mason334/J20-fighter-jet-FPV-simflight-cockpit/3d模型 2024_4_19/座舱3d模型/main screen left side panel.png

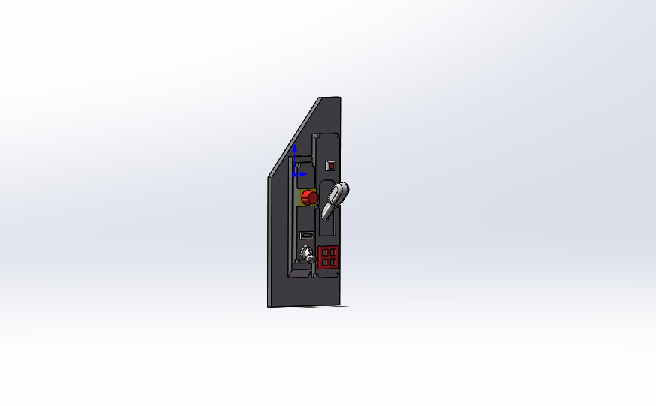
3d模型 2024_4_19/座舱3d模型/main screen left side panel.png
