mason334/J20-fighter-jet-FPV-simflight-cockpit/3d模型 2024_4_19/座舱3d模型/舱盖 适配 含进气道 座舱.png

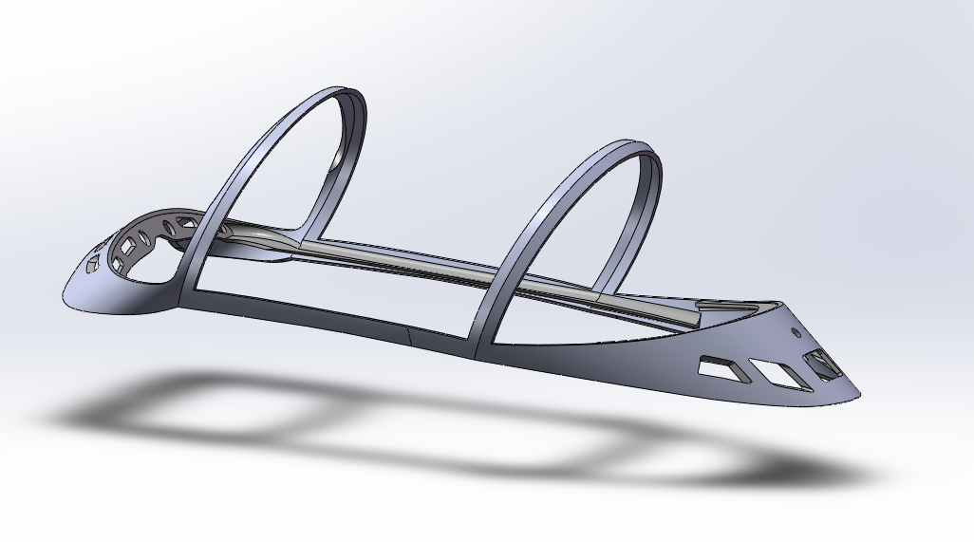
3d模型 2024_4_19/座舱3d模型/舱盖 适配 含进气道 座舱.png
