mason334/J20-fighter-jet-FPV-simflight-cockpit/3d模型 2024_4_19/座舱3d模型/装饰hud 适配 spi tft版座舱.png

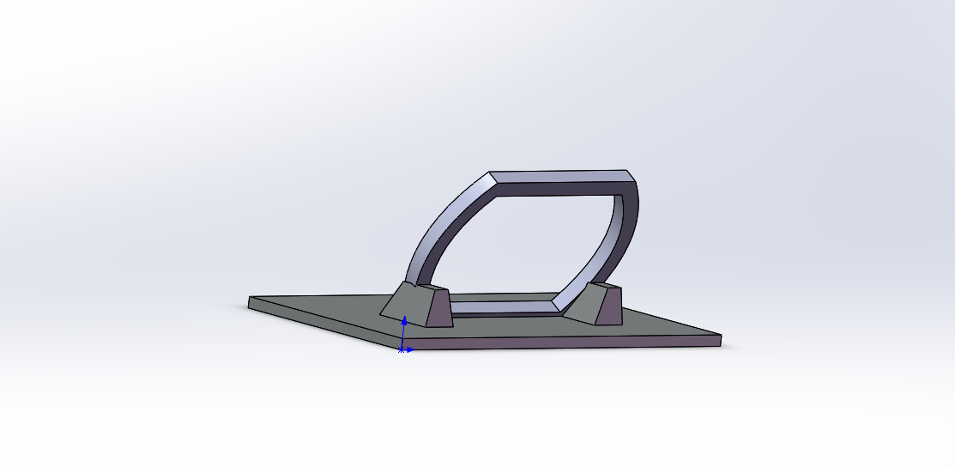
3d模型 2024_4_19/座舱3d模型/装饰hud 适配 spi tft版座舱.png
