mason334/J20-fighter-jet-FPV-simflight-cockpit/3d模型 2024_4_19/新小胖3d配件/right_airfol.png

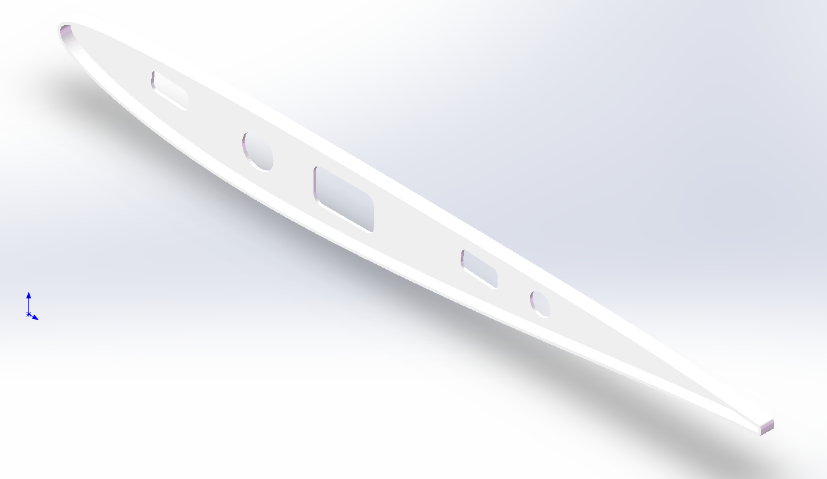
3d模型 2024_4_19/新小胖3d配件/right_airfol.png
