mason334/J20-fighter-jet-FPV-simflight-cockpit/3d模型 2024_4_19/座舱3d模型/光学hud 适配 lilygo amoled版 座舱.STEP

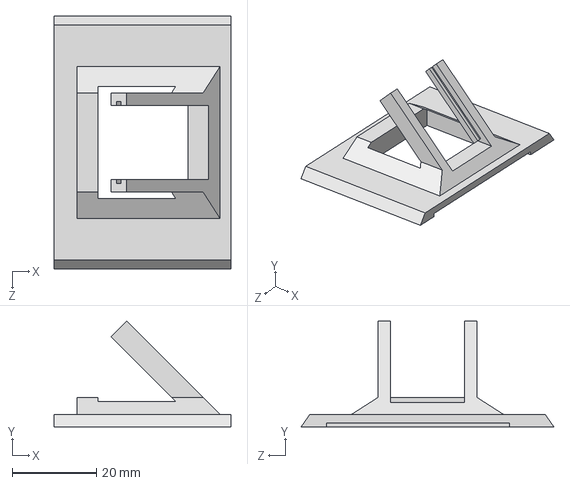
[picture p40: CAD file, 2024-04-19]
3d模型 2024_4_19/座舱3d模型/光学hud 适配 lilygo amoled版 座舱.STEP
41.9 x 25.1 x 60.0 mm
