mason334/J20-fighter-jet-FPV-simflight-cockpit/3d模型 2024_4_19/新小胖3d配件/9g servo adapter.STEP

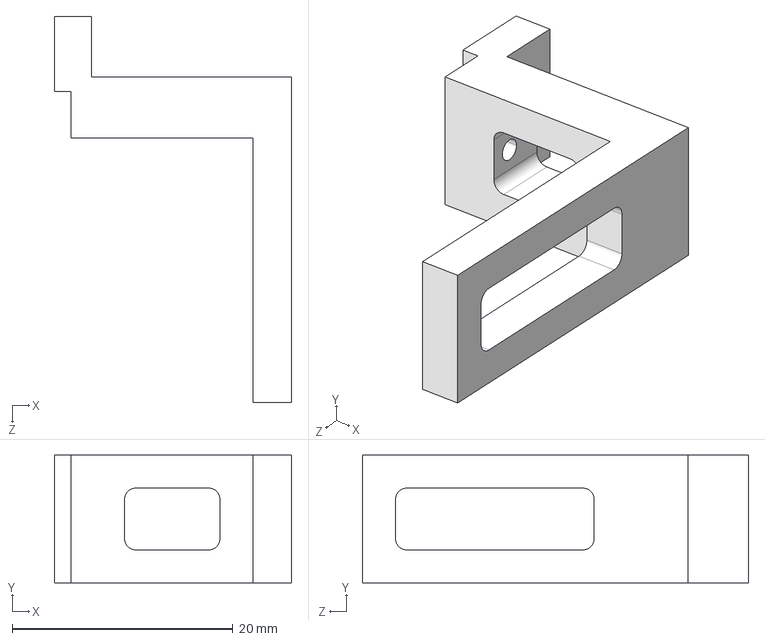
[picture p41: CAD file, 2024-04-19]
3d模型 2024_4_19/新小胖3d配件/9g servo adapter.STEP
21.5 x 11.6 x 35.0 mm
