mason334/J20-fighter-jet-FPV-simflight-cockpit/J20座舱3D模型 适配新小胖 2025-4/新小胖 j20座舱 3D模型 2025-4/舱盖.STEP

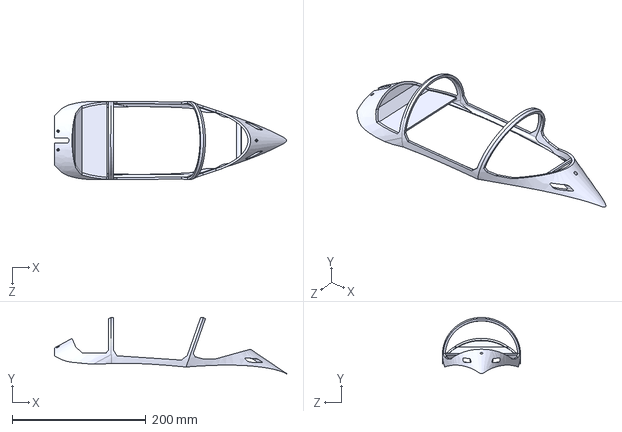
[picture p42: CAD file, 2025-04-10]
J20座舱3D模型 适配新小胖 2025-4/新小胖 j20座舱 3D模型 2025-4/舱盖.STEP
347.2 x 83.8 x 116.9 mm
