mason334/J20-fighter-jet-FPV-simflight-cockpit/3d模型 2024_4_19/座舱3d模型/left side control panel.STEP

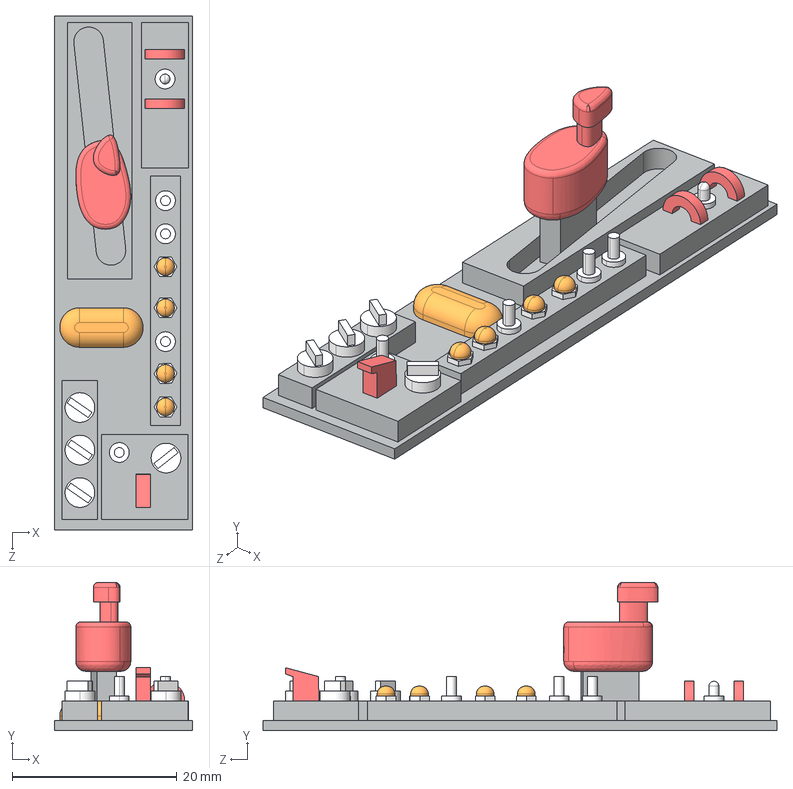
[picture p43: CAD file, 2024-04-19]
3d模型 2024_4_19/座舱3d模型/left side control panel.STEP
16.8 x 18.0 x 62.4 mm
