mason334/J20-fighter-jet-FPV-simflight-cockpit/3d模型 2024_4_19/新小胖3d配件/Motor_mount.STL

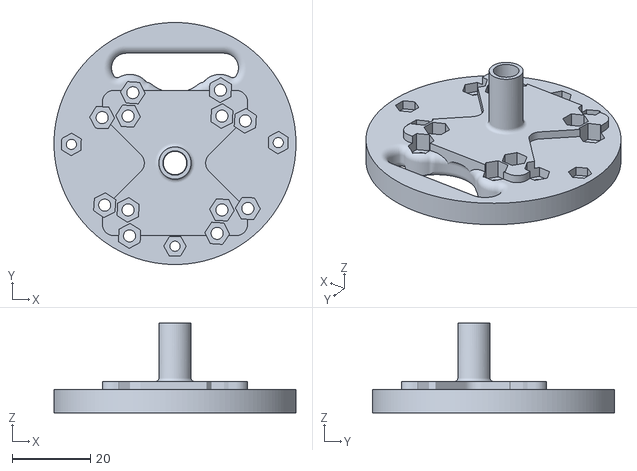
[picture p44: CAD file, 2024-04-19]
3d模型 2024_4_19/新小胖3d配件/Motor_mount.STL
62.0 x 62.0 x 23.0
