mason334/J20-fighter-jet-FPV-simflight-cockpit/3d模型 2024_4_19/座舱3d模型/舱盖 适配 含进气道 座舱.STEP

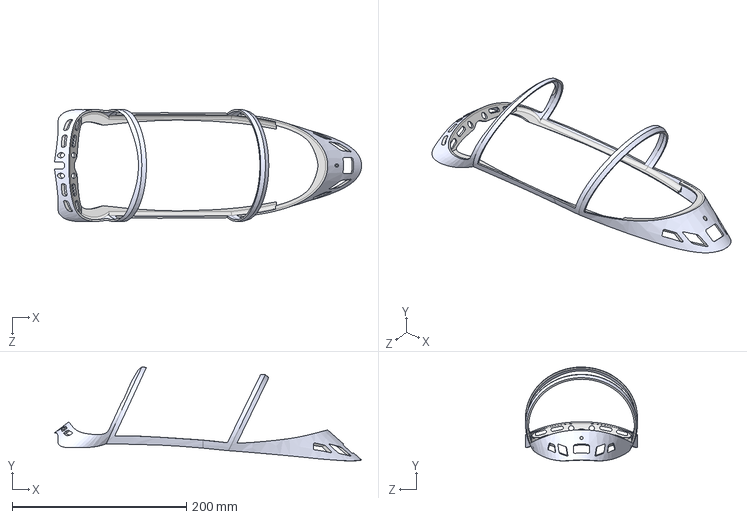
[picture p46: CAD file, 2024-04-19]
3d模型 2024_4_19/座舱3d模型/舱盖 适配 含进气道 座舱.STEP
351.9 x 107.7 x 128.3 mm
