mason334/J20-fighter-jet-FPV-simflight-cockpit/3d模型 2024_4_19/新小胖3d配件/Battery Bay.STEP

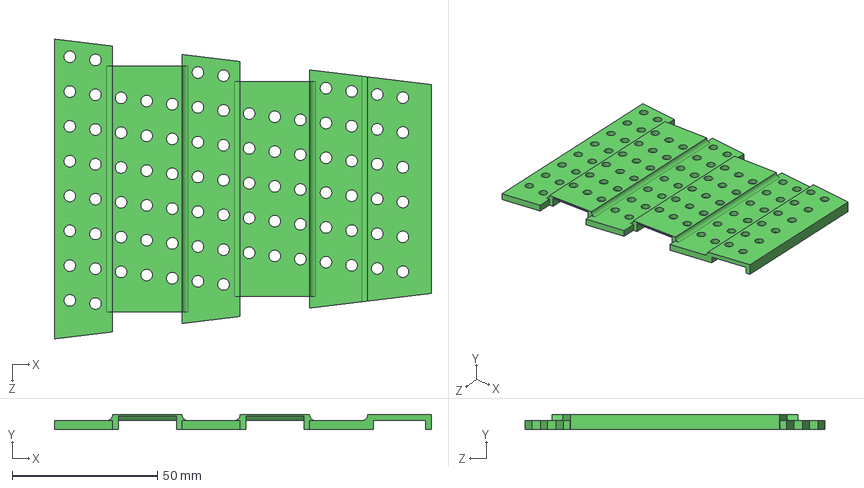
[picture p47: CAD file, 2024-04-19]
3d模型 2024_4_19/新小胖3d配件/Battery Bay.STEP
130.0 x 5.00 x 103.4 mm
