mason334/J20-fighter-jet-FPV-simflight-cockpit/3d模型 2024_4_19/座舱3d模型/right side control panel.STEP

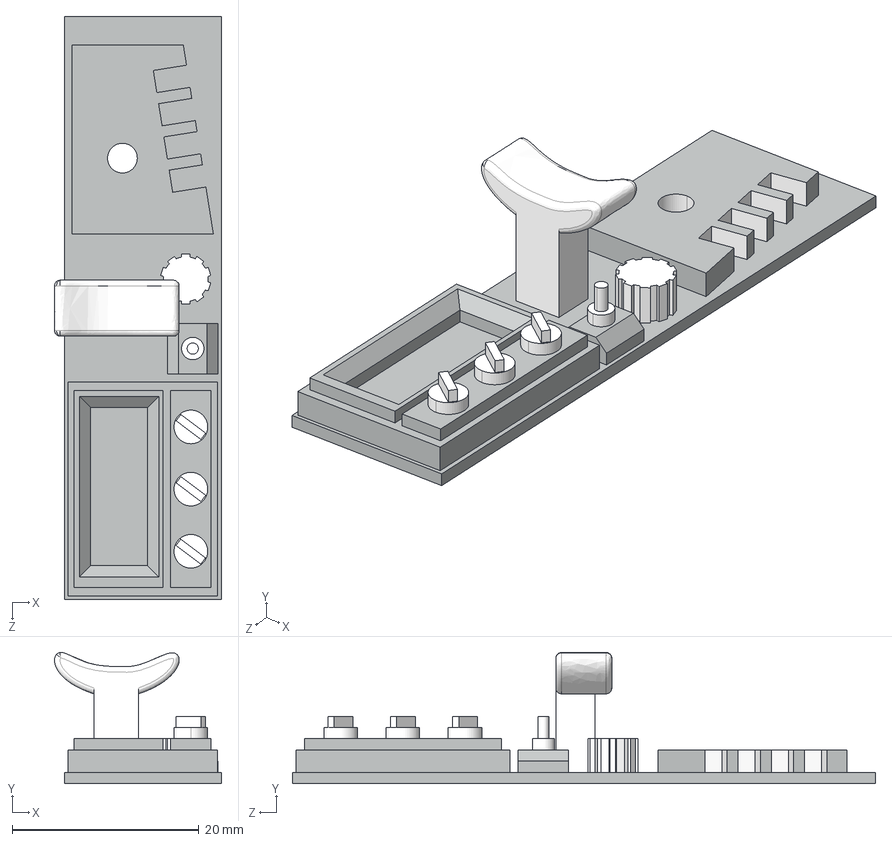
[picture p48: CAD file, 2024-04-19]
3d模型 2024_4_19/座舱3d模型/right side control panel.STEP
17.9 x 14.0 x 62.4 mm
