mason334/J20-fighter-jet-FPV-simflight-cockpit/3d模型 2024_4_19/座舱3d模型/control stick.STEP

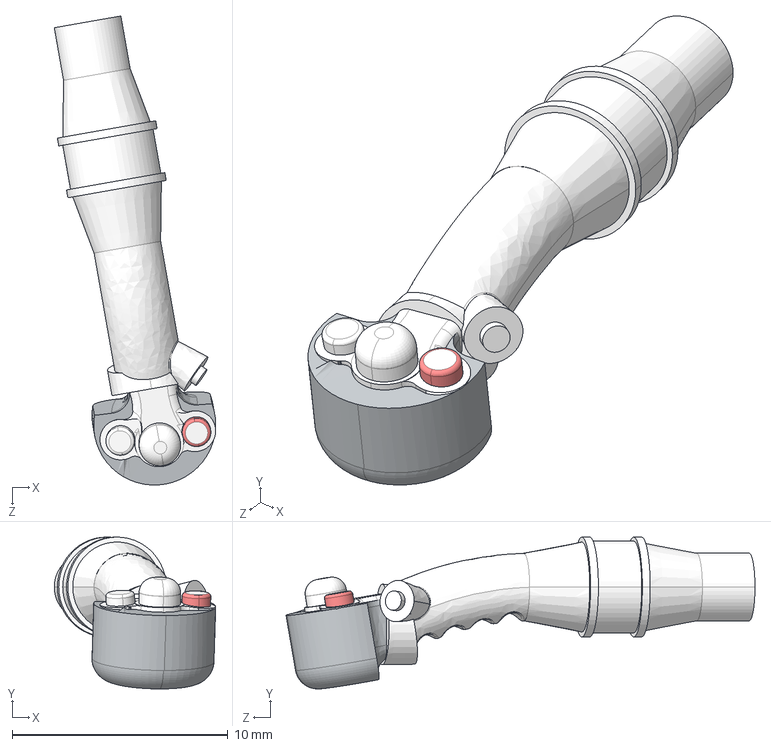
[picture p49: CAD file, 2024-04-19]
3d模型 2024_4_19/座舱3d模型/control stick.STEP
7.48 x 7.04 x 21.7 mm
