mason334/J20-fighter-jet-FPV-simflight-cockpit/3d模型 2024_4_19/新小胖3d配件/ptz servo mount.STEP

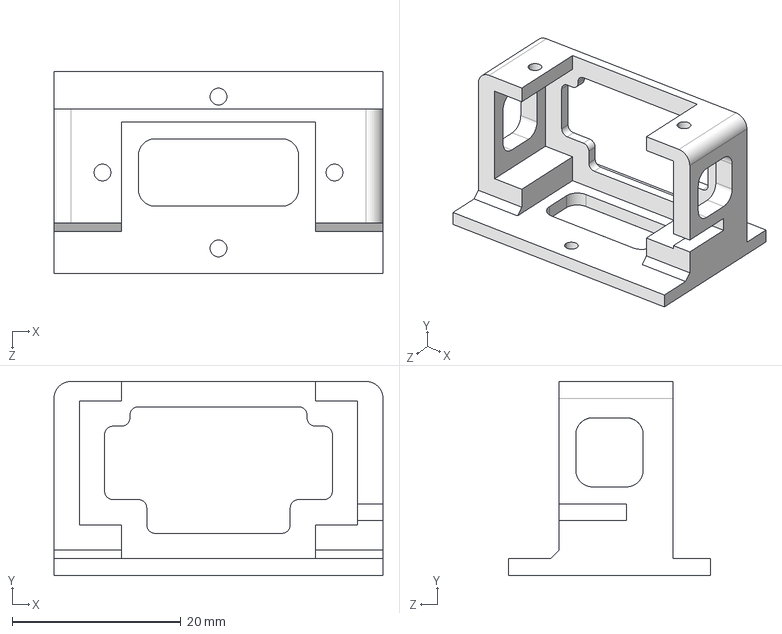
[picture p50: CAD file, 2024-04-19]
3d模型 2024_4_19/新小胖3d配件/ptz servo mount.STEP
39.0 x 23.0 x 24.0 mm
